tsmiltonAgents/20260721_countdown/docs/renders/render_bottom_3d.png

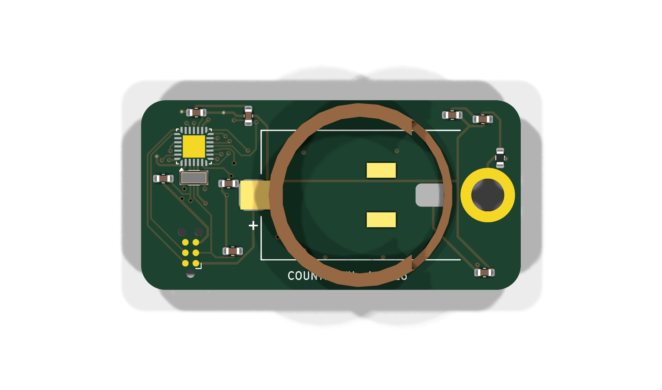
docs/renders/render_bottom_3d.png
